fablab-imperia/orto-idroponico/images/Screenshoot_ESP_web_gui_manual.png

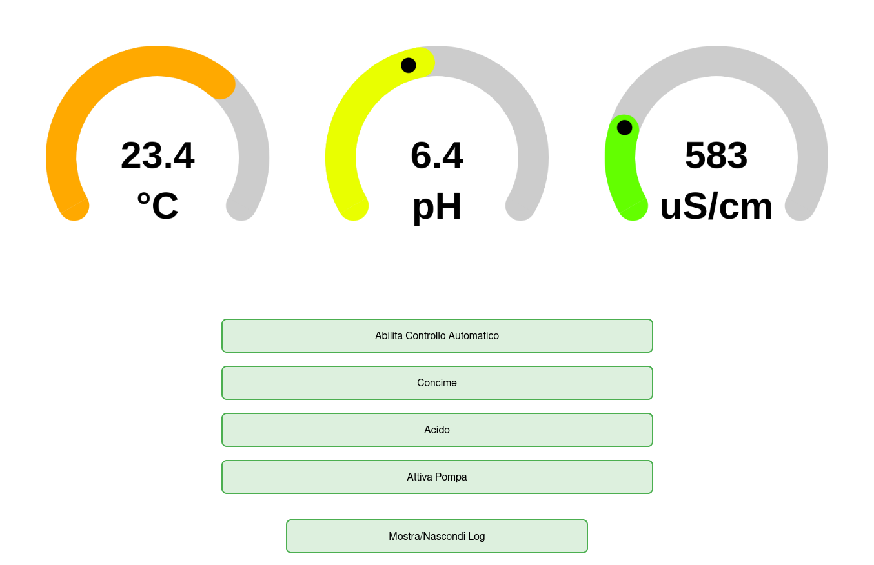
images/Screenshoot_ESP_web_gui_manual.png
